cydrollinger/low-voltage-lighting/hardware/spice/avago-asmbt.asc

D1: diode; grn
D2: diode; red
D3: diode; ble
V1: voltage; 0
Named nets: 0
.dc V1 -1 5 10m
.lib C:\\work\\Algae Light\\pspice\\Marveled Green.lib
.lib C:\\work\\Algae Light\\pspice\\Marveled Red.lib
.lib C:\\work\\Algae Light\\pspice\\Marveled Blue.lib
