cydrollinger/low-voltage-lighting/hardware/spice/on_off_mom.asc

C1: cap; 330nF
M1: pmos; BSH201
Q1: npn; FZT849
R1: res; 100k
R2: res; 10k
R3: res; 10k
R4: res; 10k
R5: res; 1e6
S1: sw
V1: voltage; 5
V2: voltage; PULSE(-1 1 200ms 1e-6 1e-6 1000ms 2000ms 10)
Named nets: 0
.tran 20000ms
.model SW SW[]
.inc BSH201.lib
