cydrollinger/low-voltage-lighting/hardware/spice/RGB_PWM.asc

R1: res; 10k
R2: res; 6.81k
R3: res; 122k
R4: res; 12.5k
R5: res; 2.5k
U1: LTC6992-1
V1: voltage; 3.3
Named nets: 0, Fout
.tran 100m
